MrTommyGuns/Binaural3D/LTspice/CicuitoLD-MC-6035W - 5 Dual Supply.asc

C1: cap; 3.3µ
C2: cap; 1p
C3: cap; 4.7µ
C4: cap; 800µ
C5: cap; 3.3µ
C7: cap; 3.3µ
C8: cap; 80µ
C9: cap; 56µ
C10: cap; 3.3µ
G1: g2; 4.546µ
R1: res; 6.8k
R2: res; 560k
R4: res; 51
R6: res; 100k
R7: res; 1k
R8: res; 33k
R9: res; 10k
R10: res; 10k
R11: res; 10k
R12: res; 10k
R13: res; 10k
R14: res; 10k
R15: res; 10k
R16: res; 10k
R17: res; 1Meg
R18: res; 100k
R19: res; 100k
U1: UniversalOpamp2
U2: UniversalOpamp2
U3: UniversalOpamp2
U4: UniversalOpamp2
V1: voltage; 110
V2: voltage; SINE(0 0.02 1000); AC 0.02
V3: voltage; 5
V4: voltage; -5
Named nets: 0, VCC, OUT, OutOpAmp, In, OutOpAmp2, VB, XLR_2, XLR_3, XLR_1, -VCC
.step oct param R2 18k 560k 1
;ac oct 100 20 20000
.tran 0 2.01 2
