MrTommyGuns/Binaural3D/LTspice/ExtractorPhantom.asc

C1: cap; 100µ
C2: cap; 100µ
D1: zener; BZX84C8V2L
R1: res; 10k
R2: res; 10k
R3: res; 10k
R4: res; 10k
R5: res; 10k
R6: res; 10k
V1: voltage; SINE(48 1.7 1000)
V2: voltage; SINE(48 1.7 1000 0 0 180)
V3: voltage; SINE(48 1.7 1000)
V4: voltage; SINE(48 1.7 1000 0 0 180)
Named nets: 0
.tran 0 2.01 2
